zr6lr/Kotinos/Build/DataRingPaddle.scad

 RingPatch = [
               [[        ], [  7, 5,  2], [  8, 0,  5], [  9.5, -6,  4], [           ]],
               [[ 3, 9, 4], [  3, 5, -1], [  3, 0,  -1], [  4, -5, -2], [  6,-11, -5]],
               [[ 0,10, 4], [  0, 5, -2], [  0, 0,  -2], [  0, -5, -3], [  0,-12, -6]],
               [[-6,10, 7], [ -6, 5, -0], [ -6, 0,  -3], [ -6, -5, -3], [ -6,-10, -7]],
               [[        ], [-11, 5, 10], [-11, -1, 12], [-11, -7,  -5], [           ]]
              ]; 

              
//uncomment for testing 

//include <PaddleSurfaceGenerator.scad>
//%PatchPaddle(RingPatch, debug=true); //comment out when redner
//color("gold", alpha=.5)PatchPaddle(RingPatch, debug=false);
